oscaromeu/FMCW-Radar/Testing/ampli/POWERS11.CSV

# Channel 1
# Trace 1
Power | Formatted Data | Formatted Data
-2.00000000000E+001 | +4.50951344603E+001 | +1.51865665357E+001
-1.92187500000E+001 | +4.50790566312E+001 | +1.52116471144E+001
-1.84375000000E+001 | +4.50726827151E+001 | +1.52351928487E+001
-1.76562500000E+001 | +4.50690425969E+001 | +1.52613131889E+001
-1.68750000000E+001 | +4.50613673300E+001 | +1.52756773957E+001
-1.60937500000E+001 | +4.50555678872E+001 | +1.52944158332E+001
-1.53125000000E+001 | +4.50582695477E+001 | +1.53212152465E+001
-1.45312500000E+001 | +4.50556417096E+001 | +1.53492725816E+001
-1.37500000000E+001 | +4.50490764386E+001 | +1.53702875242E+001
-1.29687500000E+001 | +4.50503405595E+001 | +1.53933060736E+001
-1.21875000000E+001 | +4.50435028047E+001 | +1.54296293869E+001
-1.14062500000E+001 | +4.50314186173E+001 | +1.54656649591E+001
-1.06250000000E+001 | +4.50133551086E+001 | +1.55094450594E+001
-9.84375000000E+000 | +4.49976467125E+001 | +1.55606128826E+001
-9.06250000000E+000 | +4.49709219796E+001 | +1.56371129033E+001
-8.28125000000E+000 | +4.49330093634E+001 | +1.57325963698E+001
-7.50000000000E+000 | +4.48811782491E+001 | +1.58564781718E+001
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
