oscaromeu/FMCW-Radar/Testing/vco/vco.pdf

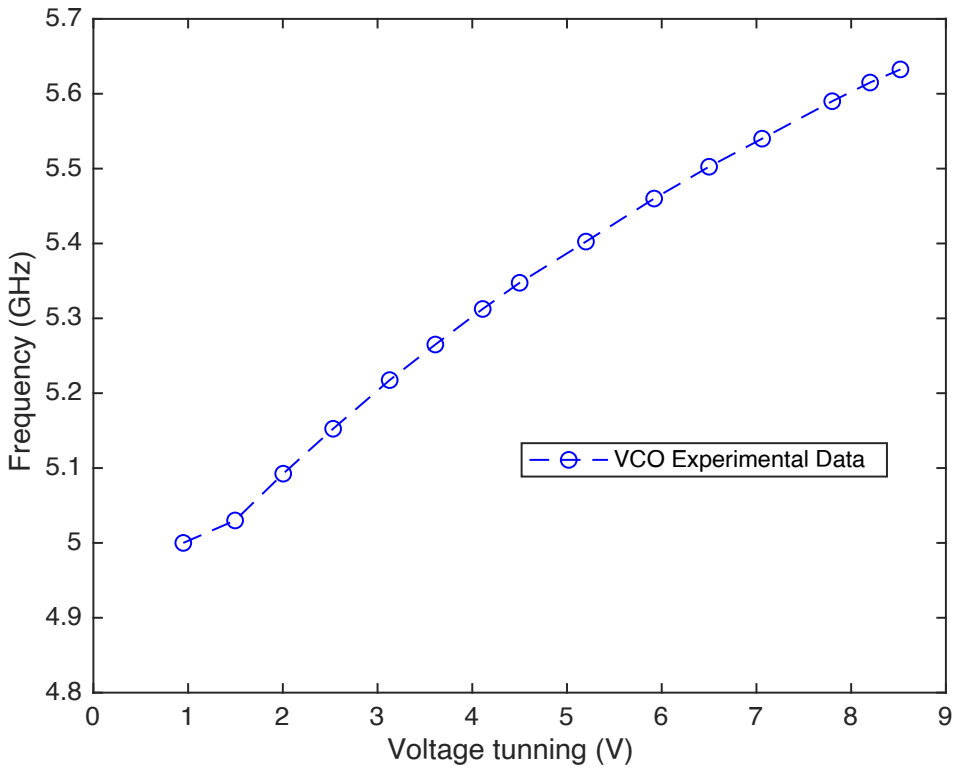
[picture p21: page 1]
Voltage tunning (V); Frequency (GHz)

VCO Experimental Data
