oscaromeu/FMCW-Radar/Hardware/FMCWRadar/doc/FMCWRadar_sch.pdf

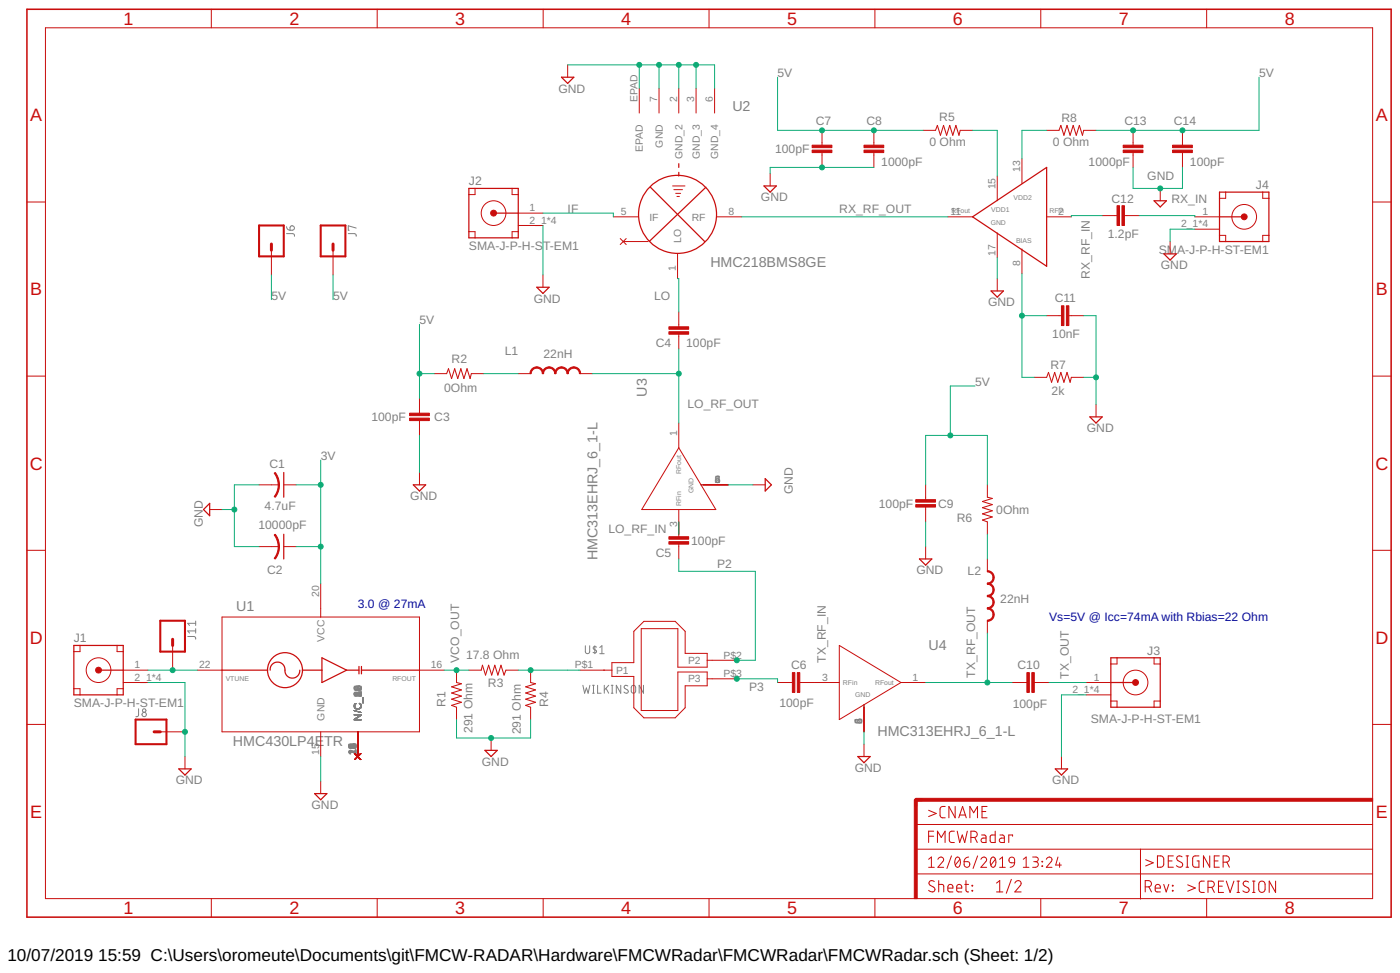
[picture p22: page 1]

Vs=5V @ Icc=74mA with Rbias=22 Ohm

10/07/2019 15:59 C:\Users\oromeute\Documents\git\FMCW-RADAR\Hardware\FMCWRadar\FMCWRadar\FMCWRadar.sch (Sheet: 1/2)

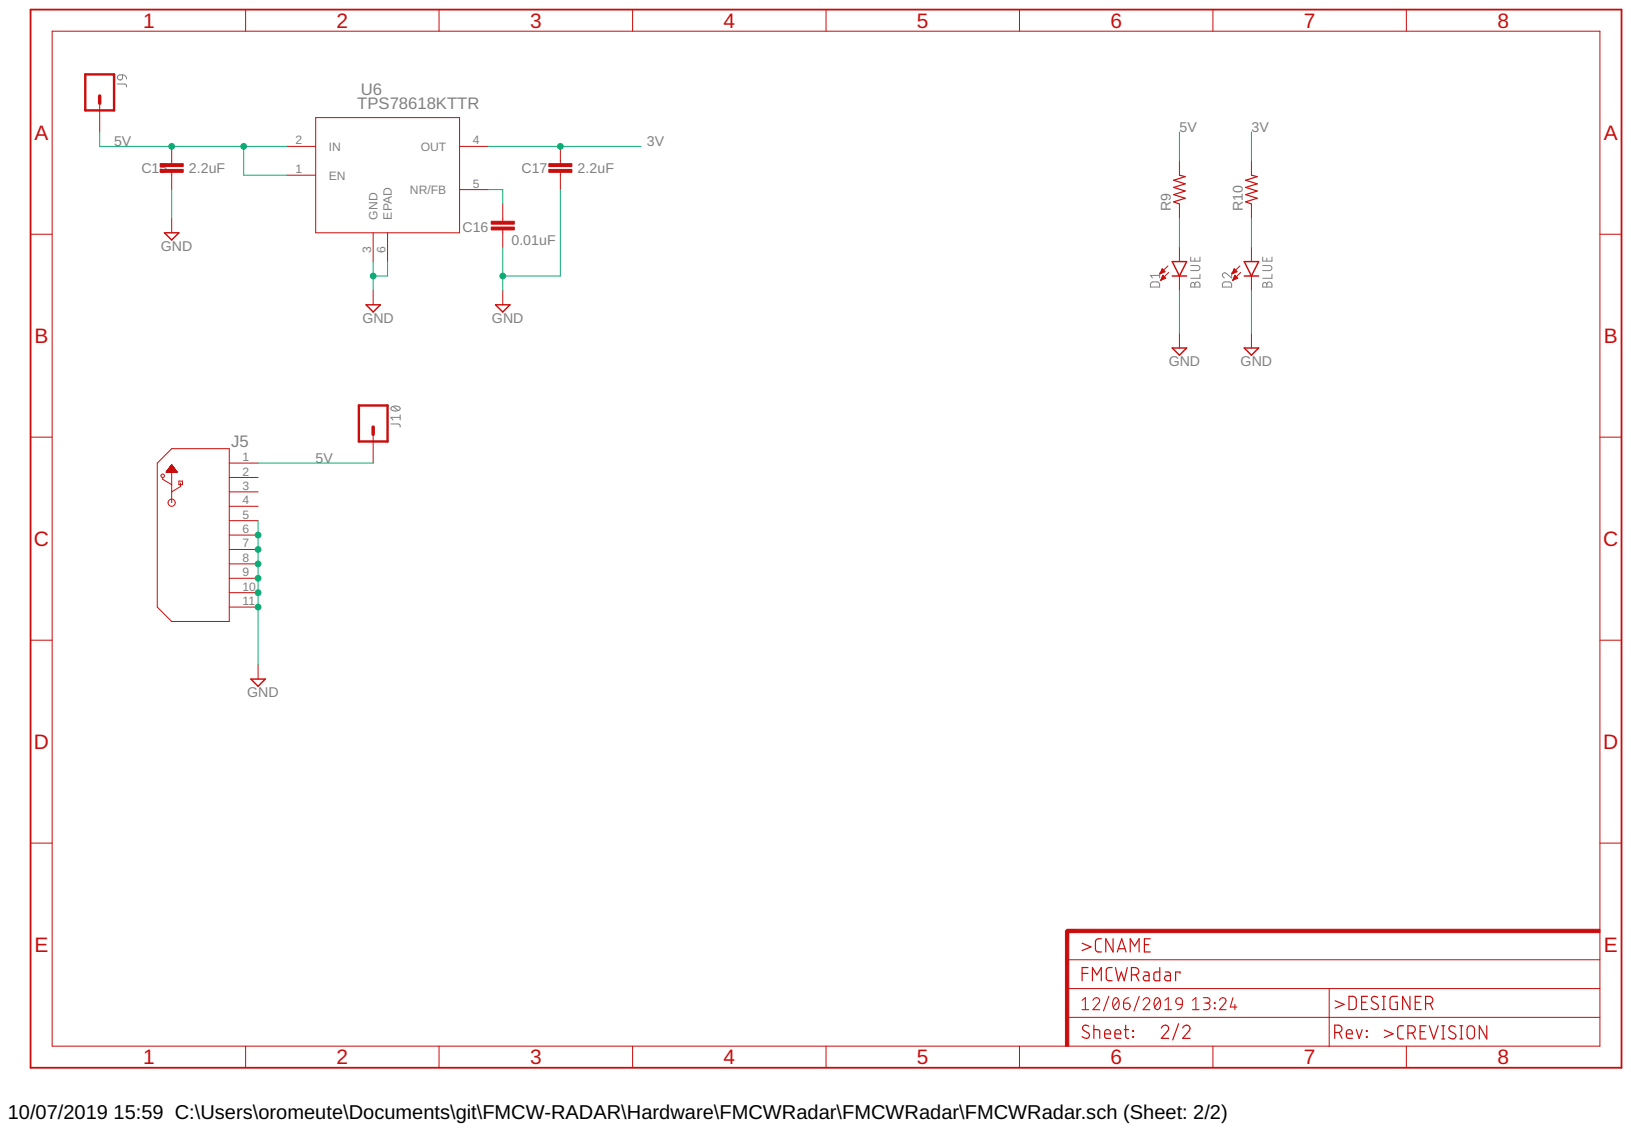
[picture p23: page 2]

10/07/2019 15:59 C:\Users\oromeute\Documents\git\FMCW-RADAR\Hardware\FMCWRadar\FMCWRadar\FMCWRadar.sch (Sheet: 2/2)
