oscaromeu/FMCW-Radar/Hardware/FMCWRadar/FMCWRadar/FMCWRadar.pdf

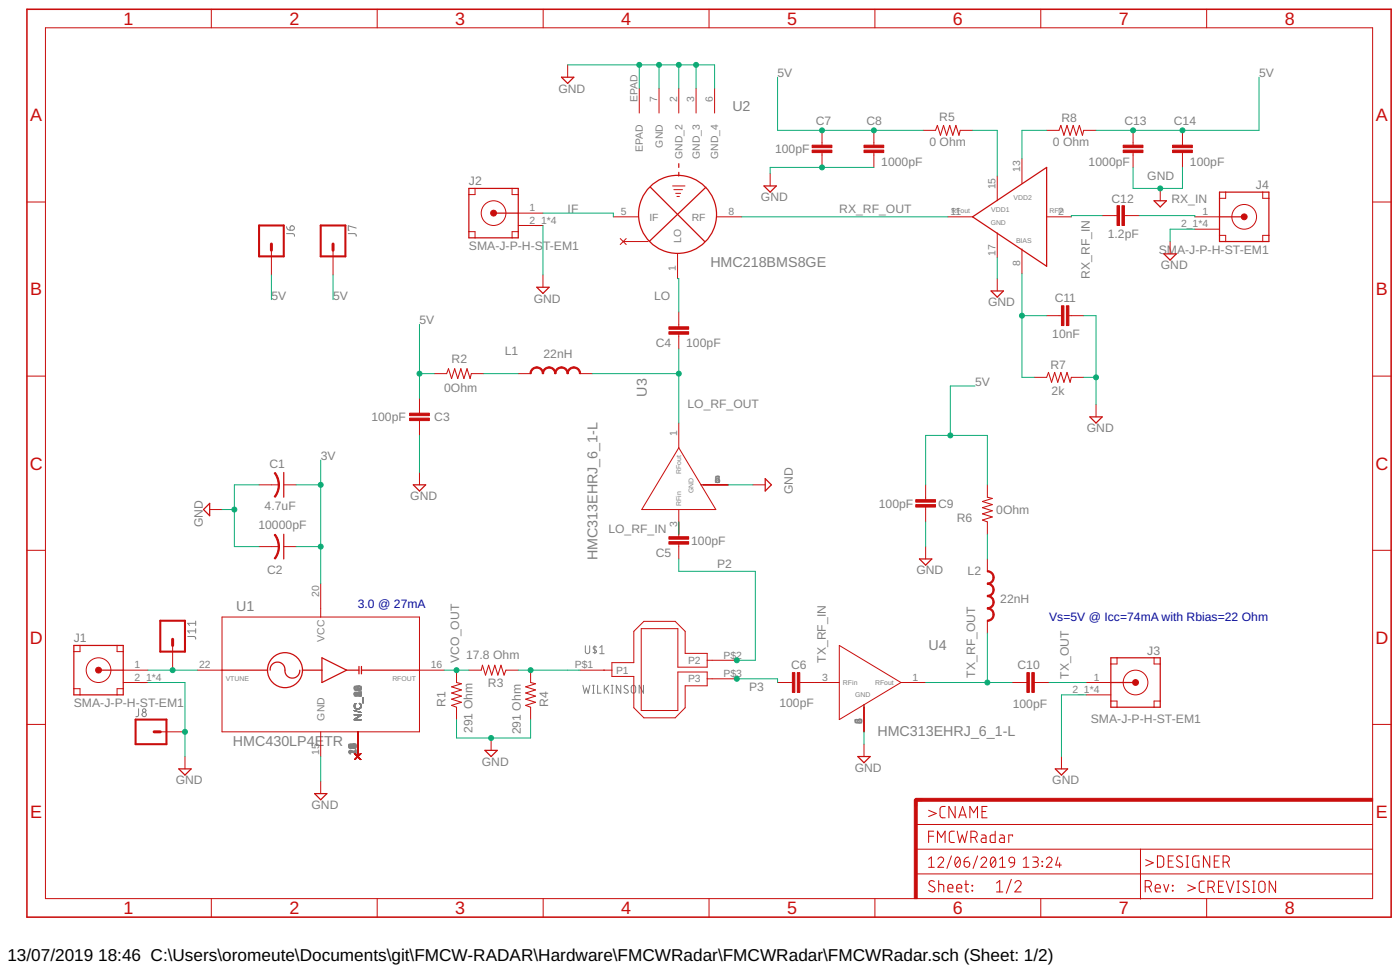
[picture p24: page 1]

Vs=5V @ Icc=74mA with Rbias=22 Ohm

13/07/2019 18:46 C:\Users\oromeute\Documents\git\FMCW-RADAR\Hardware\FMCWRadar\FMCWRadar\FMCWRadar.sch (Sheet: 1/2)
