oscaromeu/FMCW-Radar/Testing/vivaldi/vivaldi1.pdf

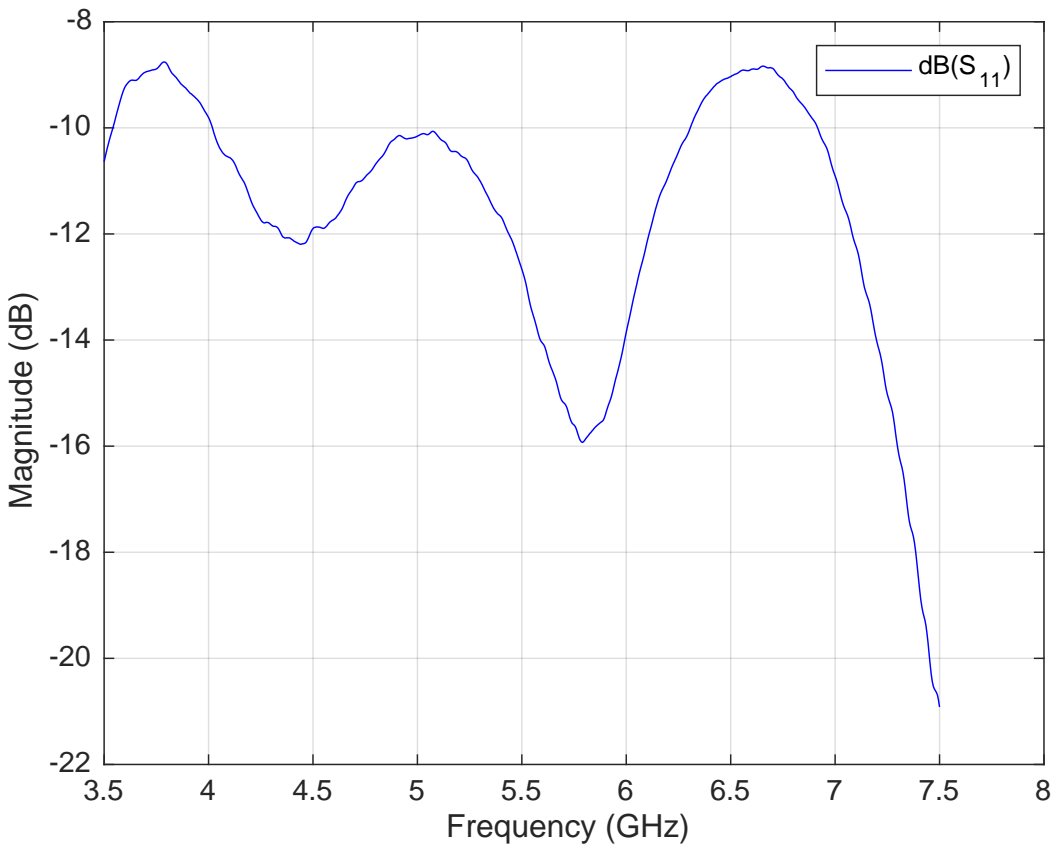
[picture p28: page 1]
Frequency (GHz); Magnitude (dB)
