oscaromeu/FMCW-Radar/Testing/vivaldi/vivaldi12_s11_s12_metal.pdf

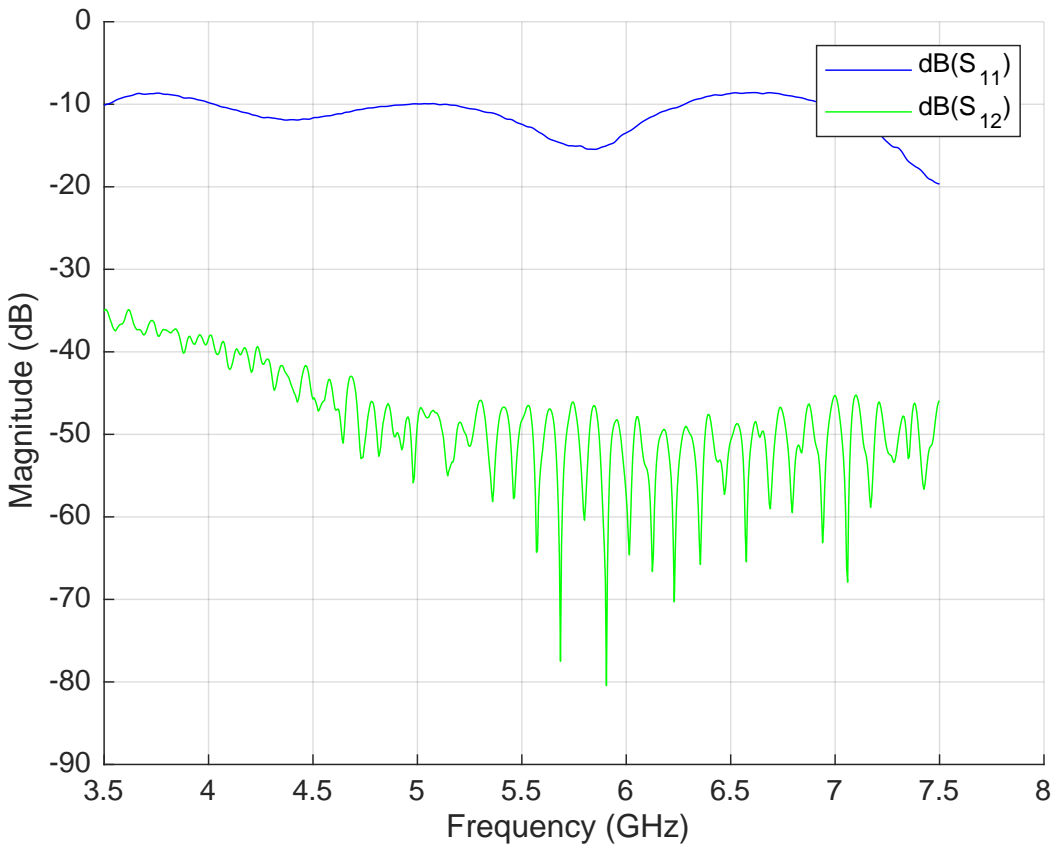
[picture p29: page 1]
Frequency (GHz); Magnitude (dB)

dB(S11 | ) )
dB(S12
