oscaromeu/FMCW-Radar/Testing/vivaldi/vivaldi12_s11_s12_sinmetal.pdf

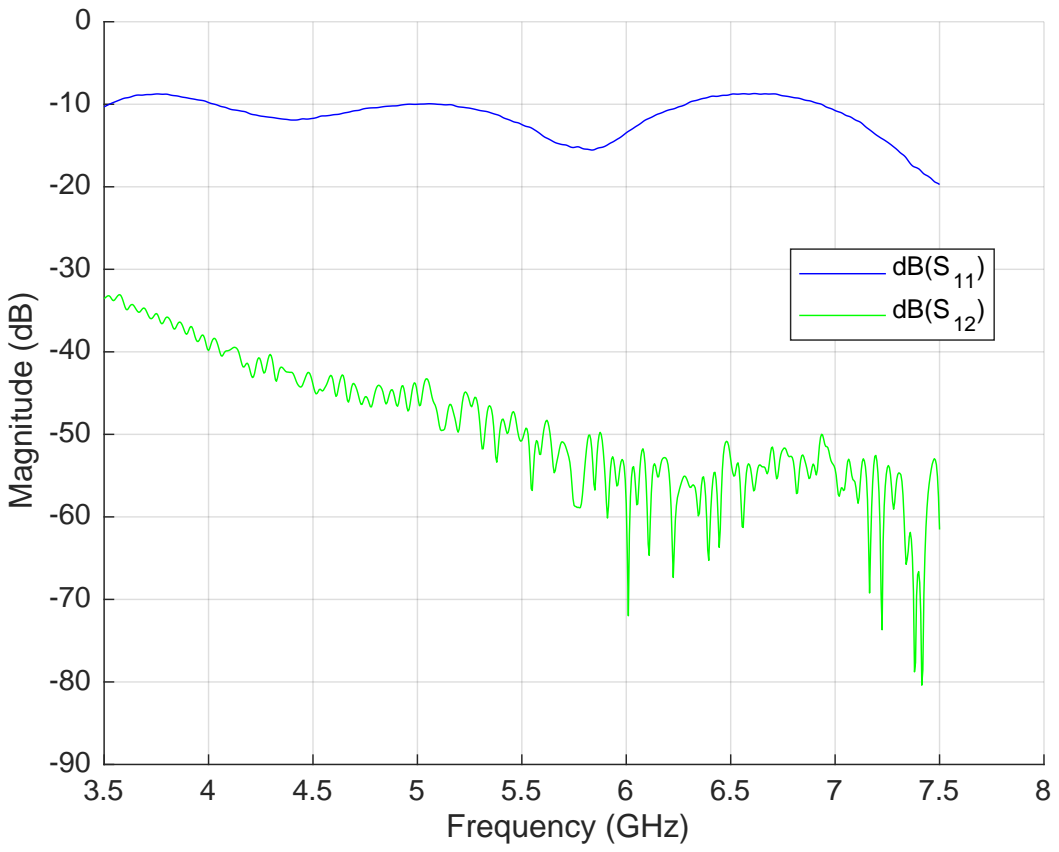
[picture p30: page 1]
Frequency (GHz); Magnitude (dB)

dB(S11)
dB(S12)
