oscaromeu/FMCW-Radar/Testing/vivaldi/vivaldi12_s12_s11.pdf

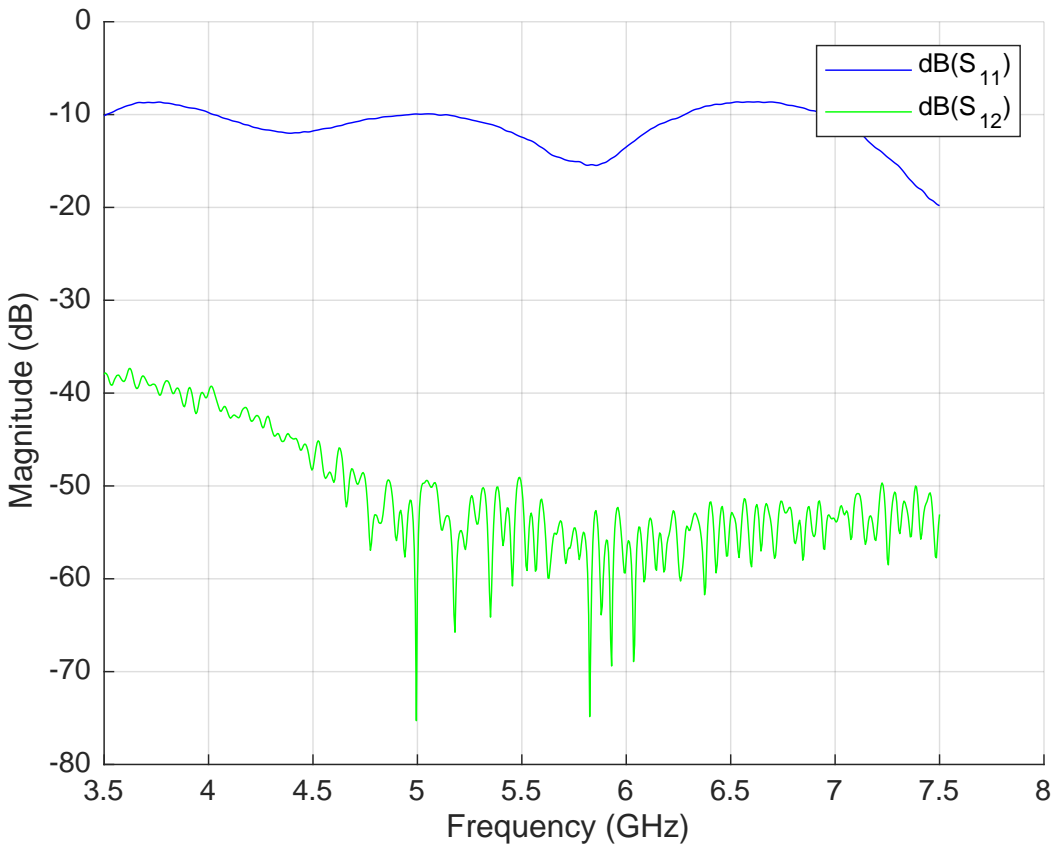
[picture p31: page 1]
Frequency (GHz); Magnitude (dB)
