oscaromeu/FMCW-Radar/Testing/vivaldi/vivaldi12_s12_s11_frontal.pdf

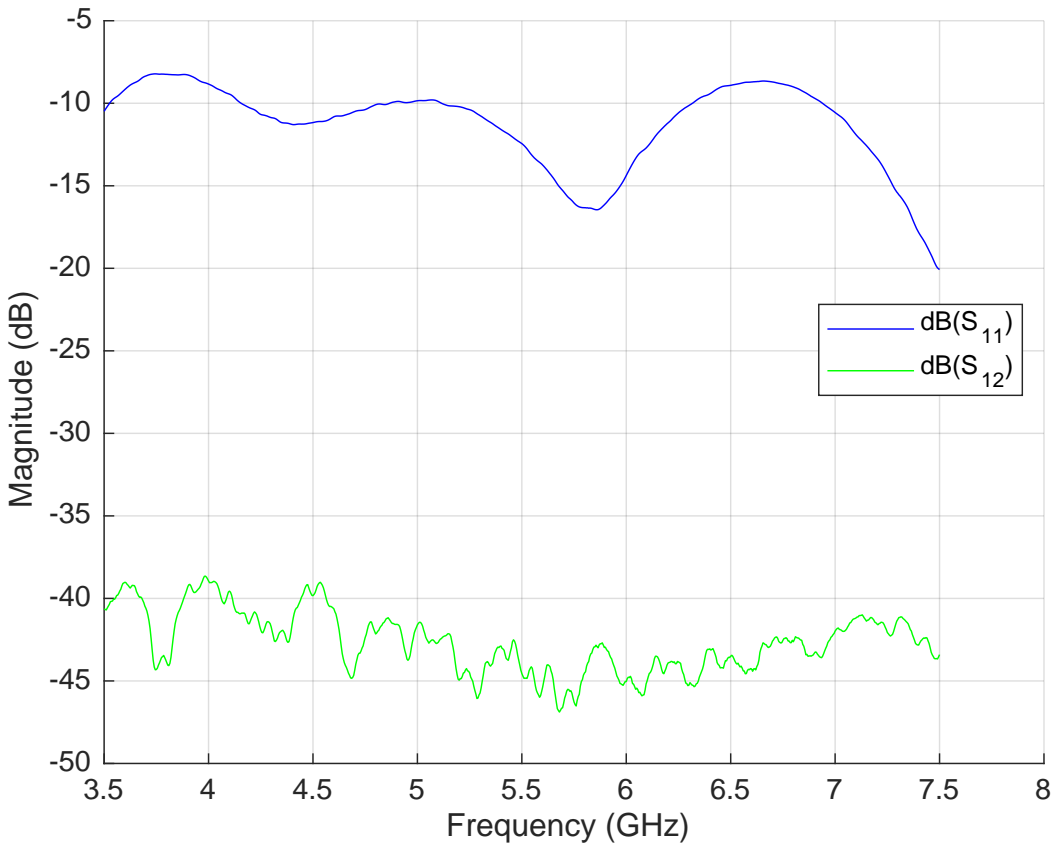
[picture p32: page 1]
Frequency (GHz); Magnitude (dB)

dB(S11)
dB(S12)
