oscaromeu/FMCW-Radar/Testing/vivaldi/vivaldi12_s21_s22.pdf

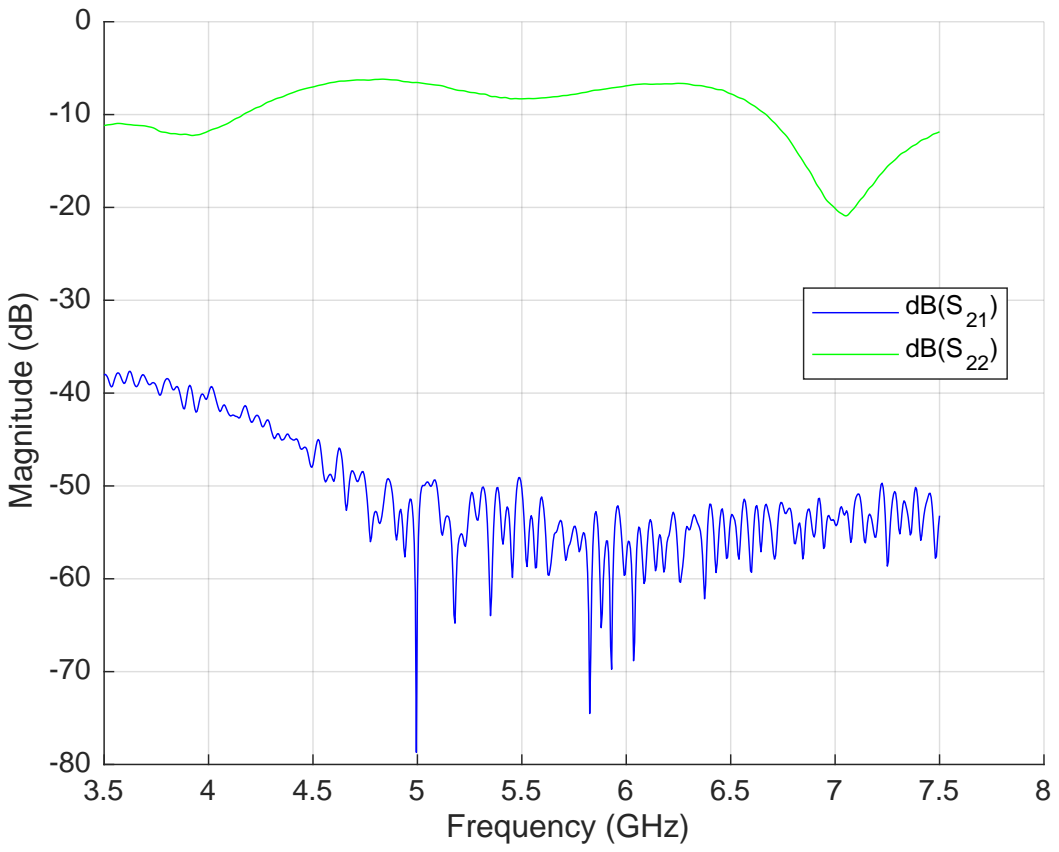
[picture p33: page 1]
Frequency (GHz); Magnitude (dB)
