oscaromeu/FMCW-Radar/Testing/vivaldi/vivaldi12_s21_s22_frontal.pdf

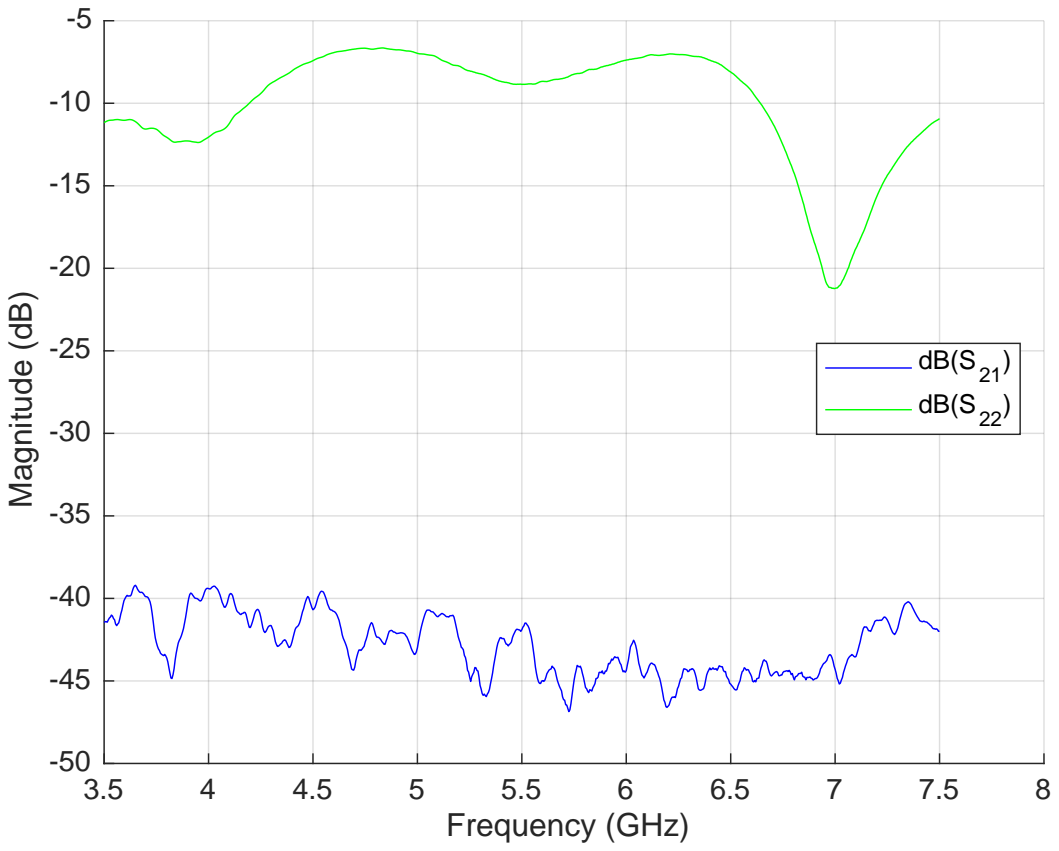
[picture p34: page 1]
Frequency (GHz); Magnitude (dB)
