oscaromeu/FMCW-Radar/Testing/vivaldi/vivaldi12_s21_s22_sin_metal.pdf

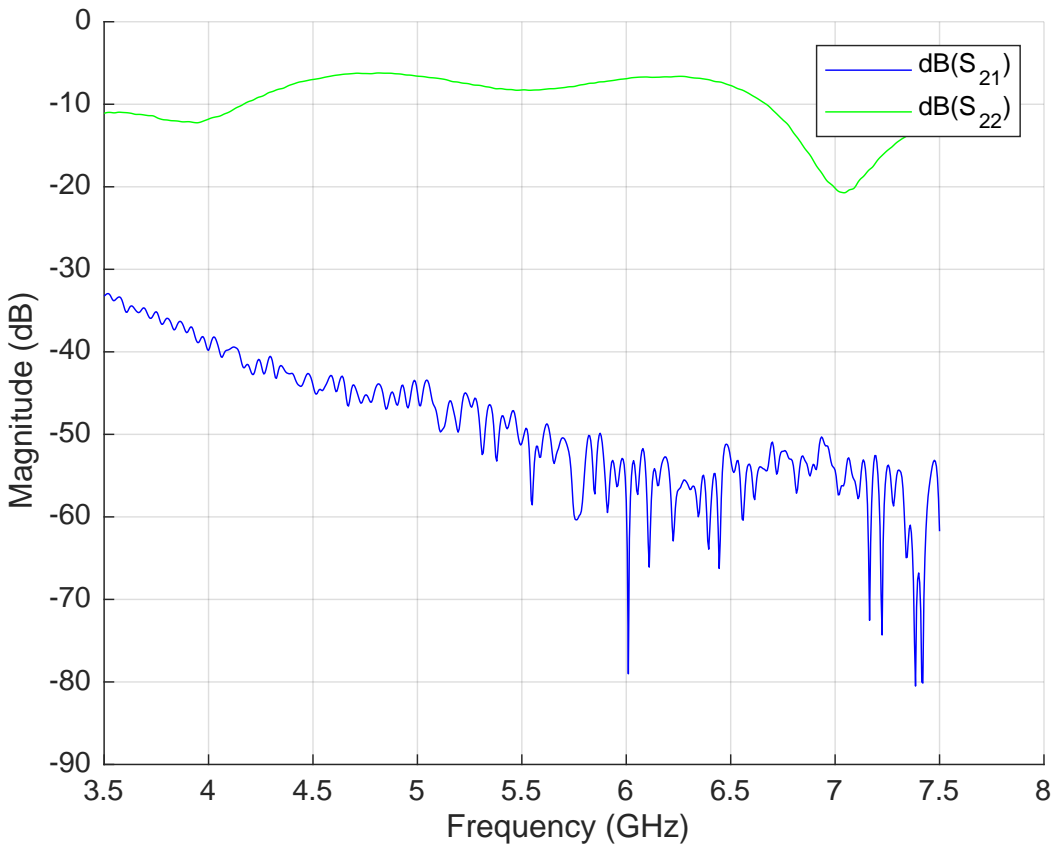
[picture p36: page 1]
Frequency (GHz); Magnitude (dB)

dB(S21 | ) )
dB(S22
