oscaromeu/FMCW-Radar/Testing/vivaldi/vivaldi2.pdf

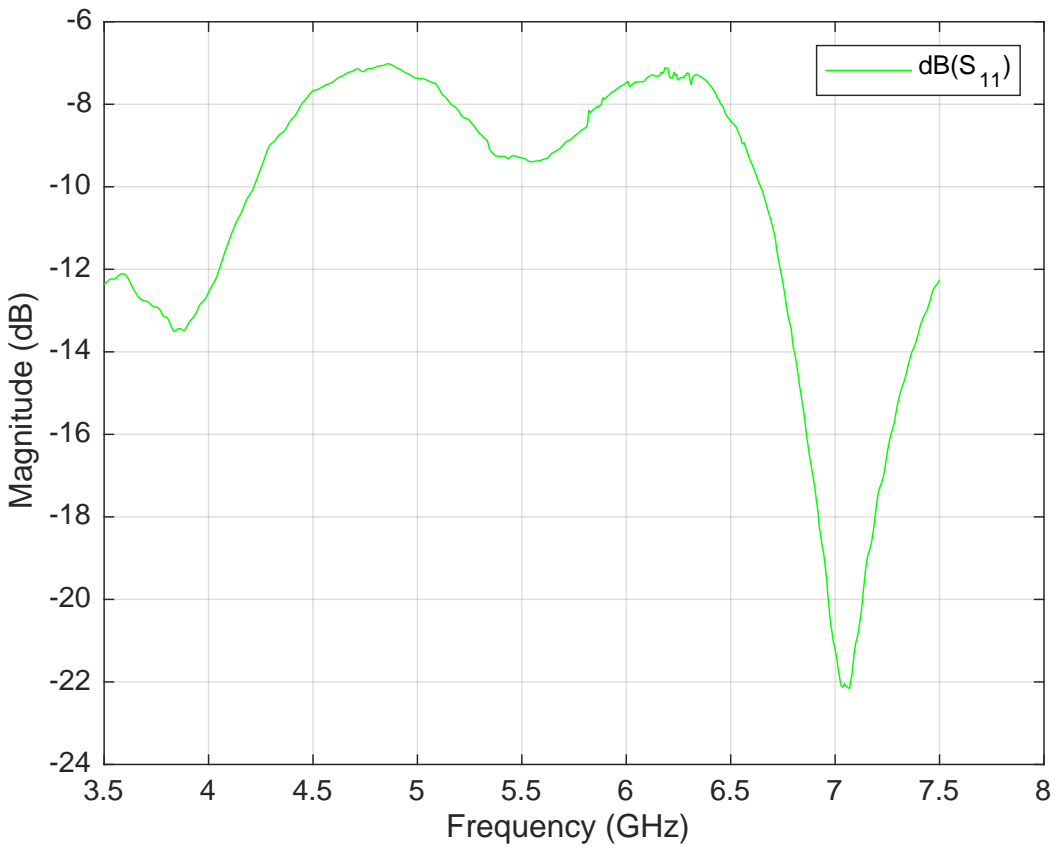
[picture p37: page 1]
Frequency (GHz); Magnitude (dB)
