oscaromeu/FMCW-Radar/Testing/vivaldi/vivaldi3.pdf

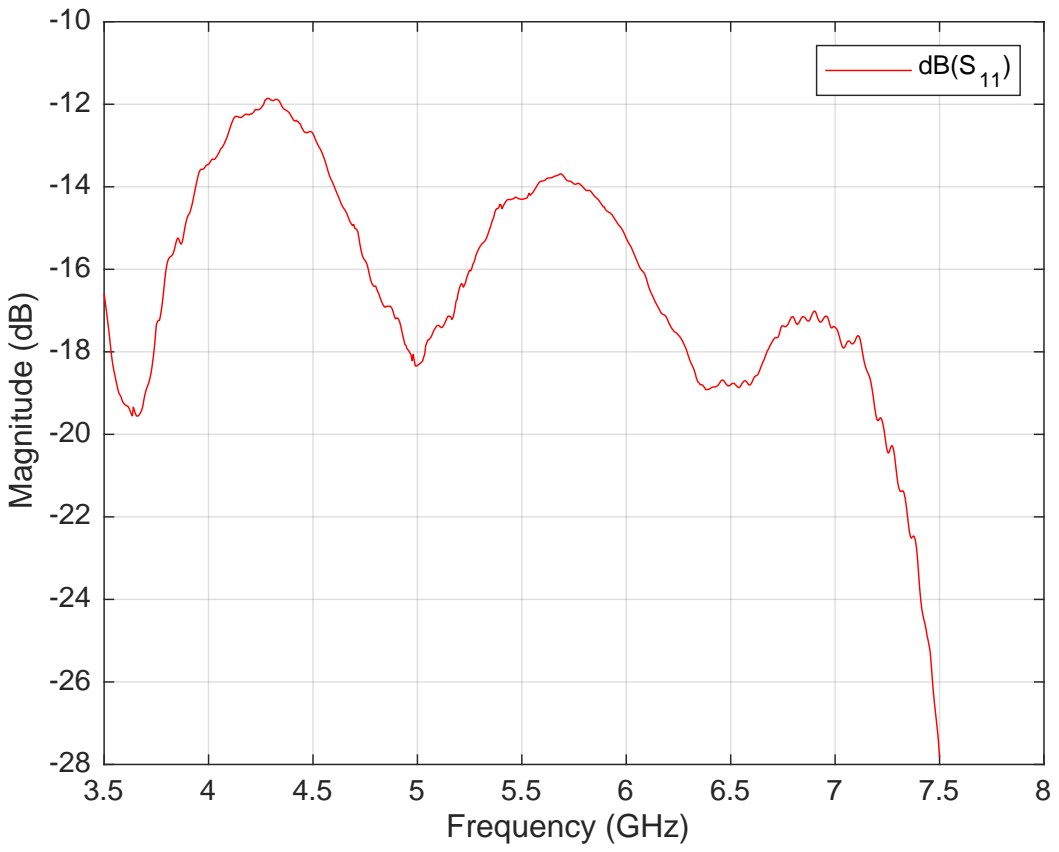
[picture p38: page 1]
Frequency (GHz); Magnitude (dB)
