oscaromeu/FMCW-Radar/Testing/wilkinson/insertionLoss.pdf

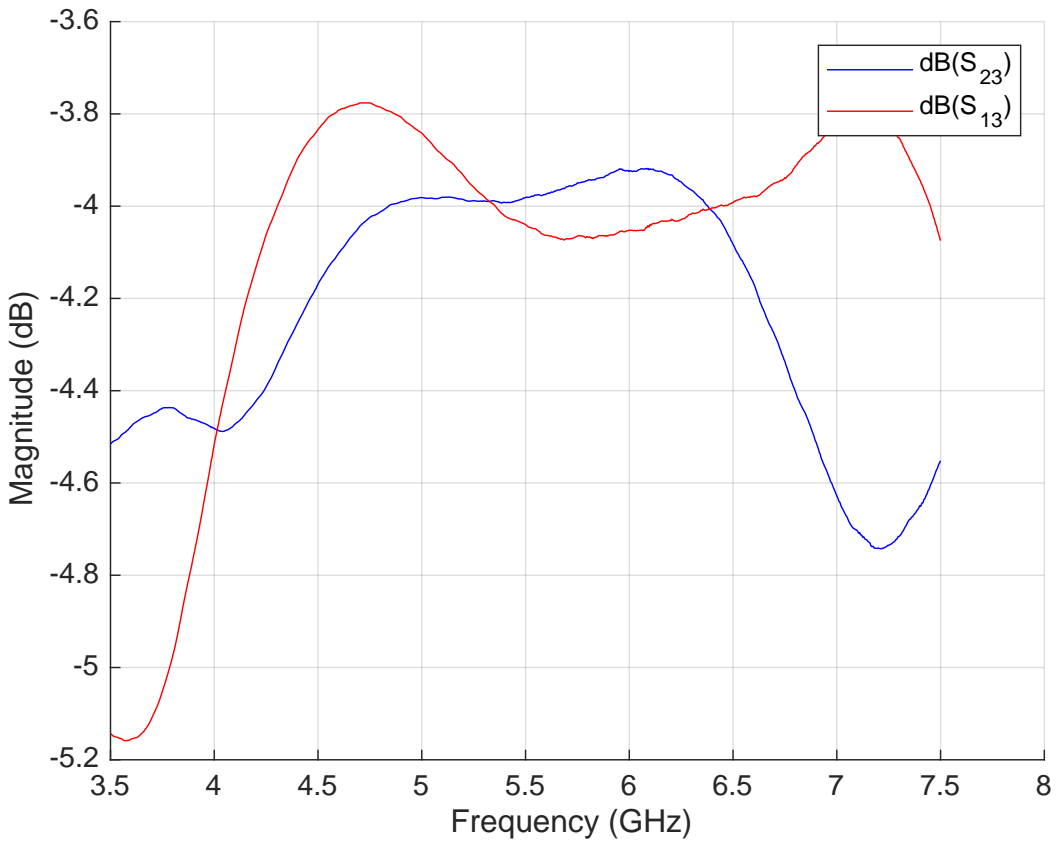
[picture p39: page 1]
Frequency (GHz); Magnitude (dB)
