oscaromeu/FMCW-Radar/Testing/wilkinson/isolation.pdf

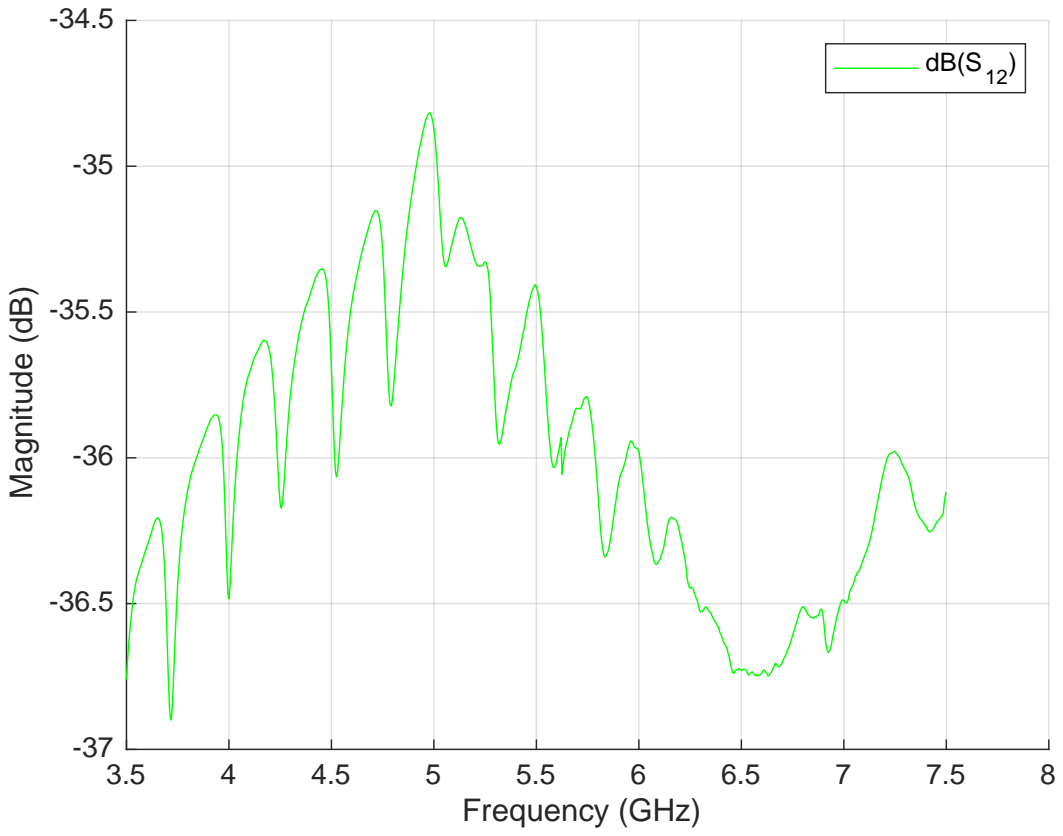
[picture p40: page 1]
Frequency (GHz); Magnitude (dB)
