oscaromeu/FMCW-Radar/Testing/wilkinson/returnLoss.pdf

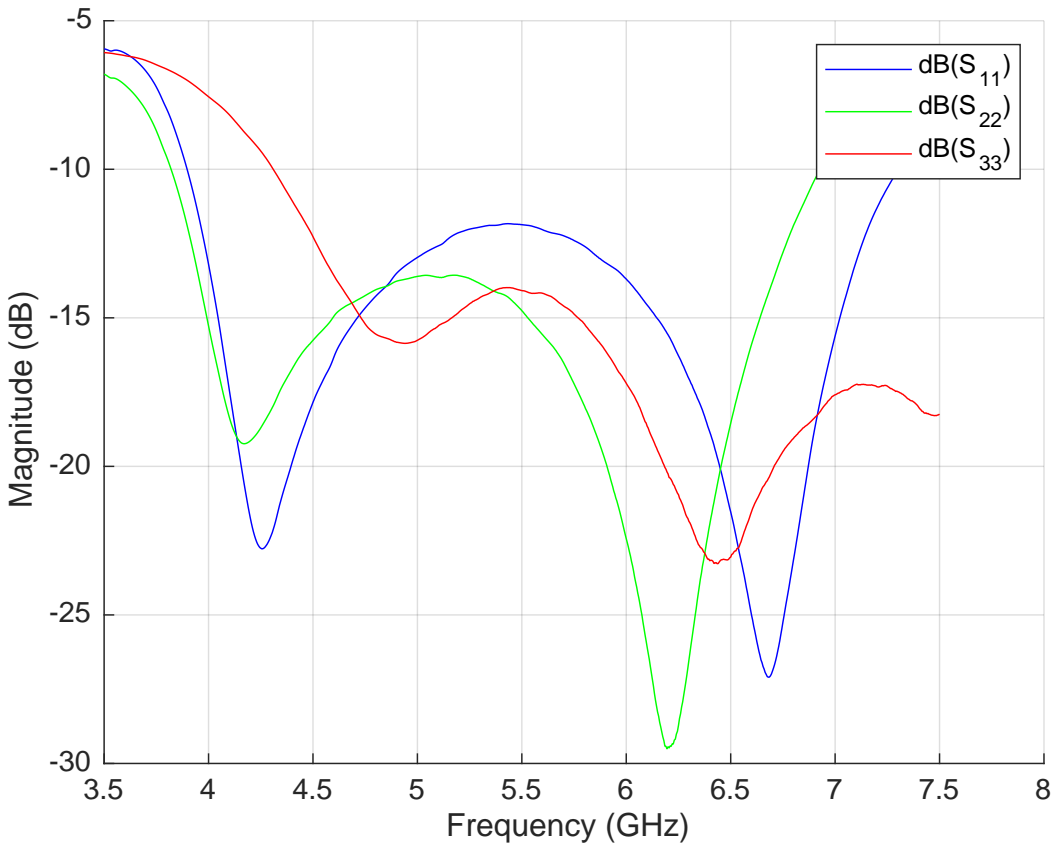
[picture p41: page 1]
Frequency (GHz); Magnitude (dB)
