oscaromeu/FMCW-Radar/Testing/wilkinson/wilkinson.pdf

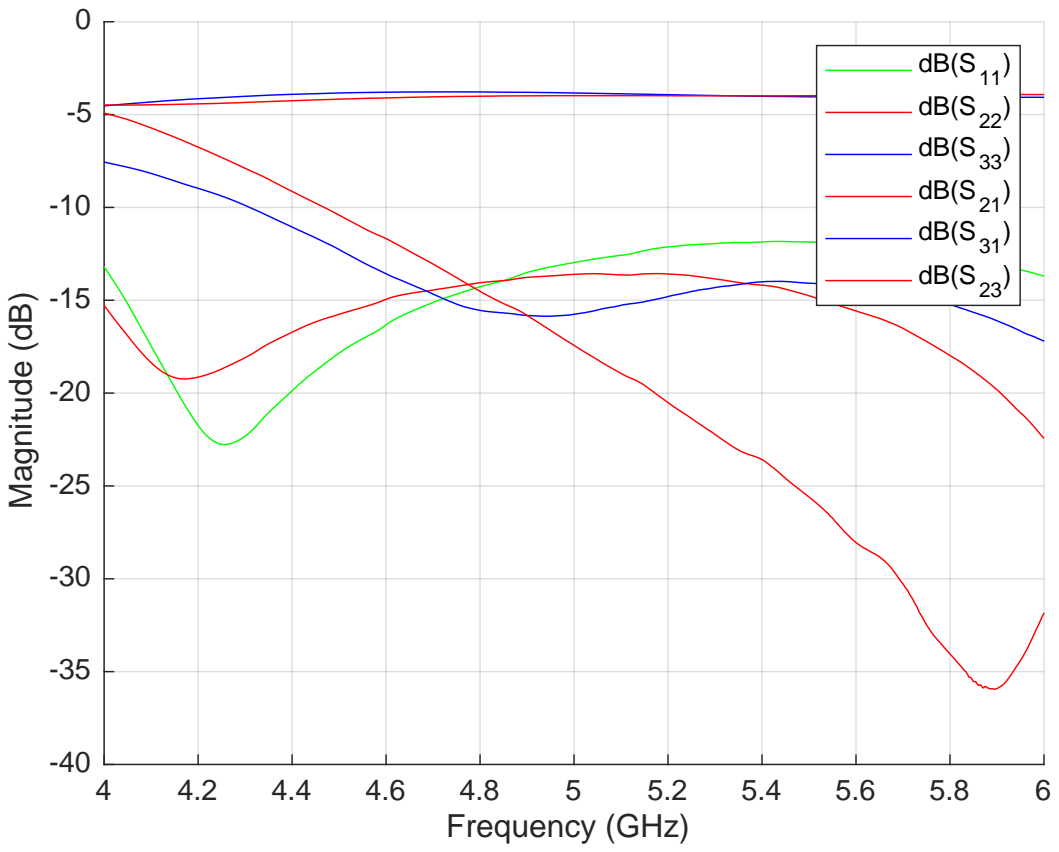
[picture p42: page 1]
Frequency (GHz); Magnitude (dB)
