oscaromeu/FMCW-Radar/Testing/wilkinson/wloads12.pdf

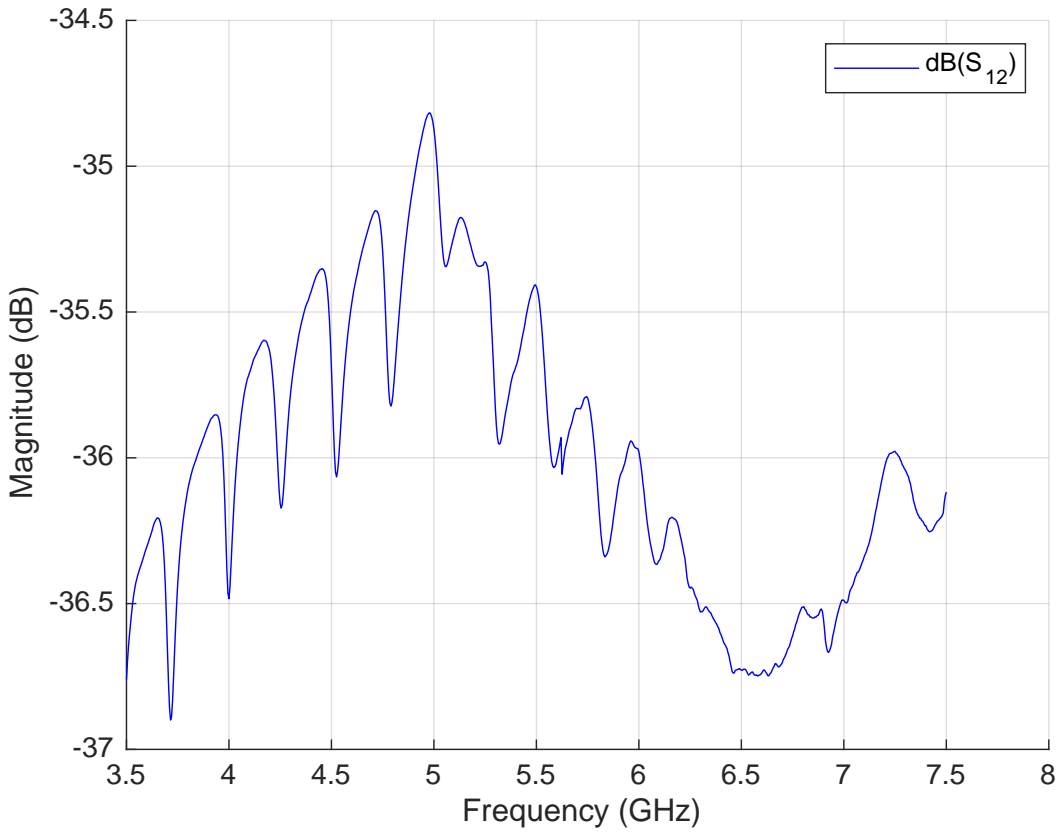
[picture p43: page 1]
Frequency (GHz); Magnitude (dB)
