oscaromeu/FMCW-Radar/Testing/wilkinson/wloads13.pdf

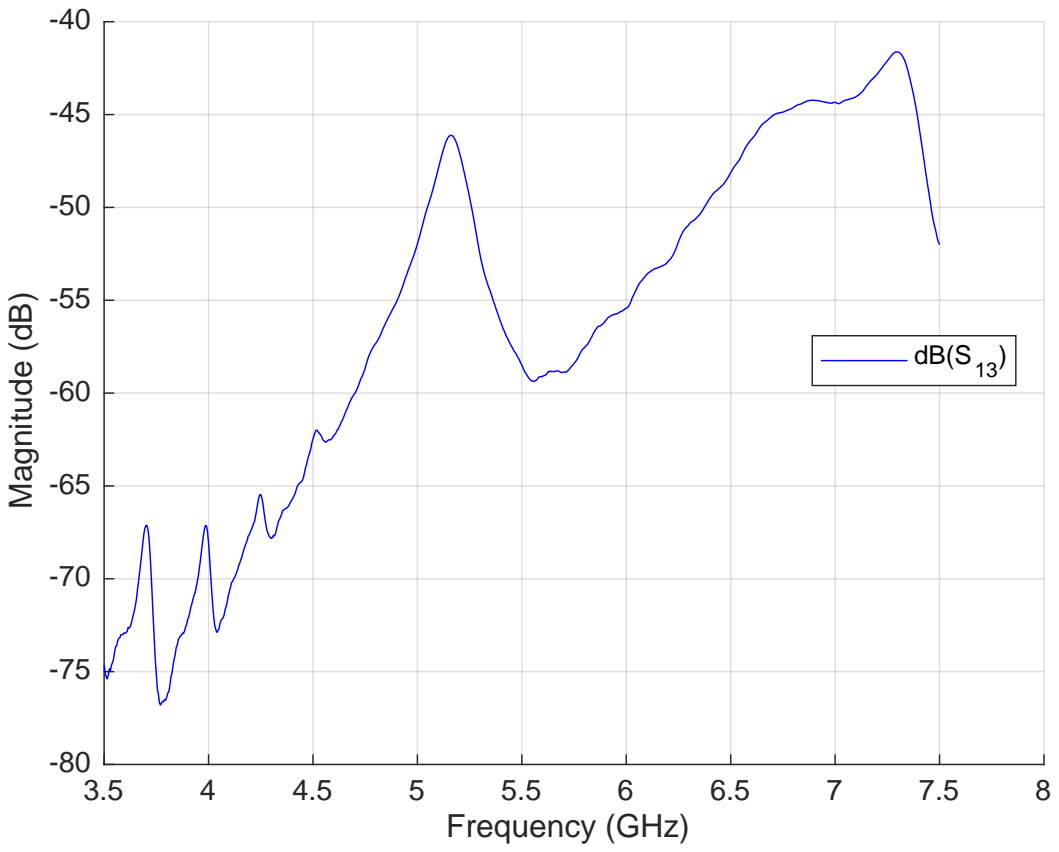
[picture p44: page 1]
Frequency (GHz); Magnitude (dB)
