oscaromeu/FMCW-Radar/Testing/wilkinson/wloads21.pdf

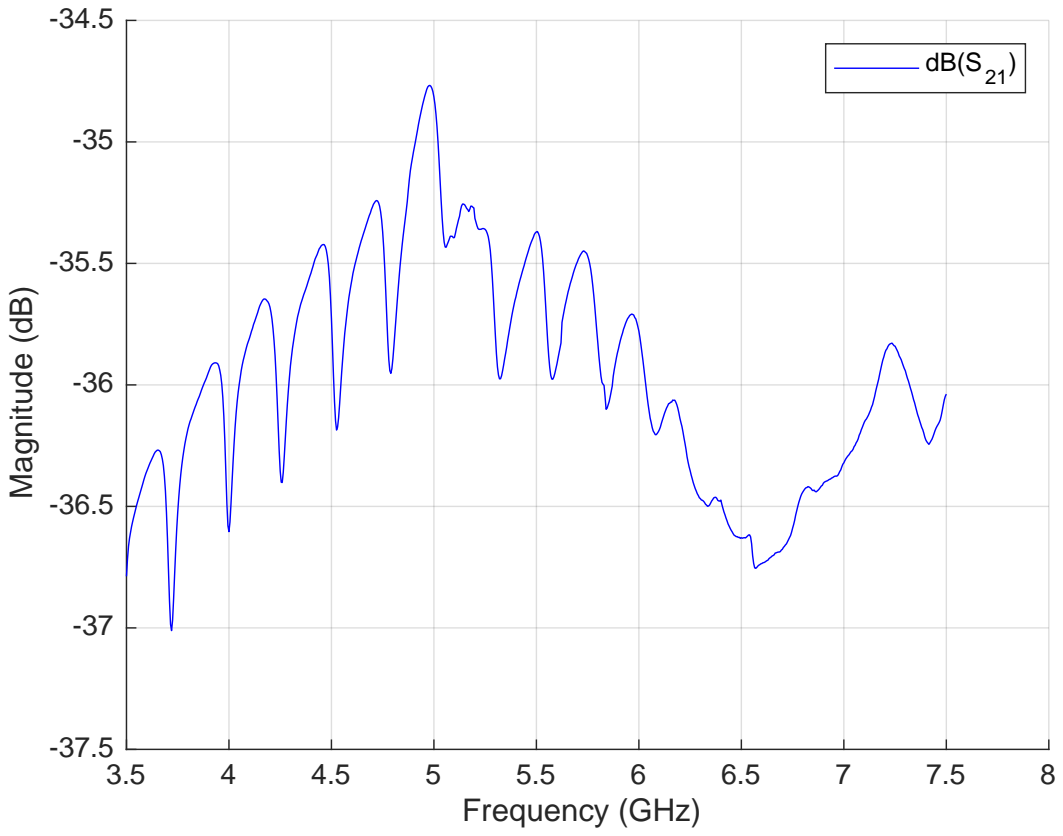
[picture p45: page 1]
Frequency (GHz); Magnitude (dB)
