oscaromeu/FMCW-Radar/Testing/wilkinson/wloads22.pdf

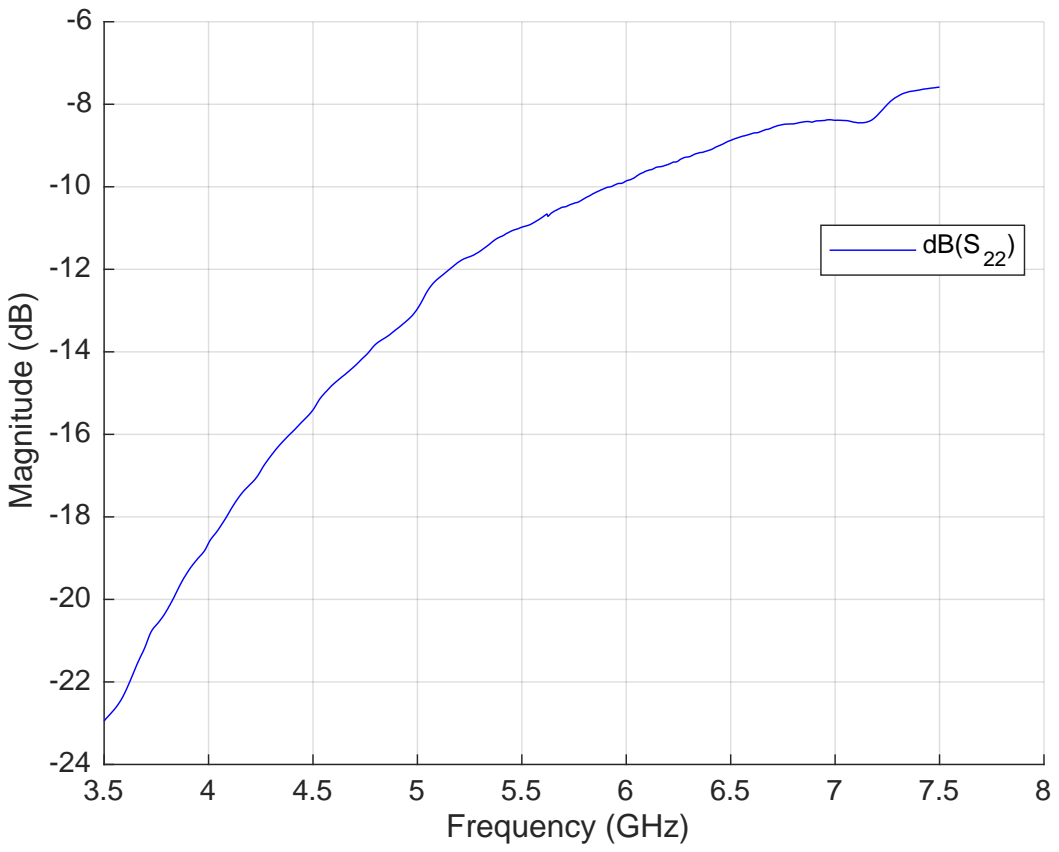
[picture p46: page 1]
Frequency (GHz); Magnitude (dB)
