oscaromeu/FMCW-Radar/Testing/wilkinson/wloads23.pdf

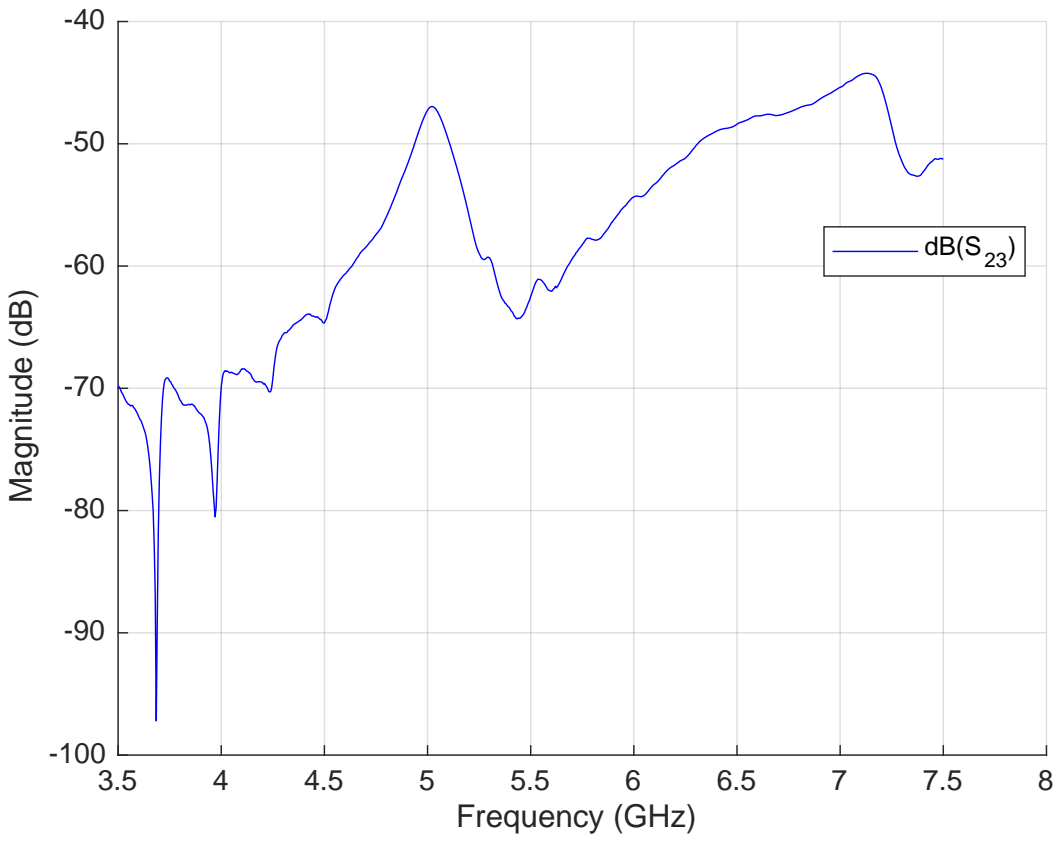
[picture p47: page 1]
Frequency (GHz); Magnitude (dB)
