oscaromeu/FMCW-Radar/Testing/wilkinson/wloads31.pdf

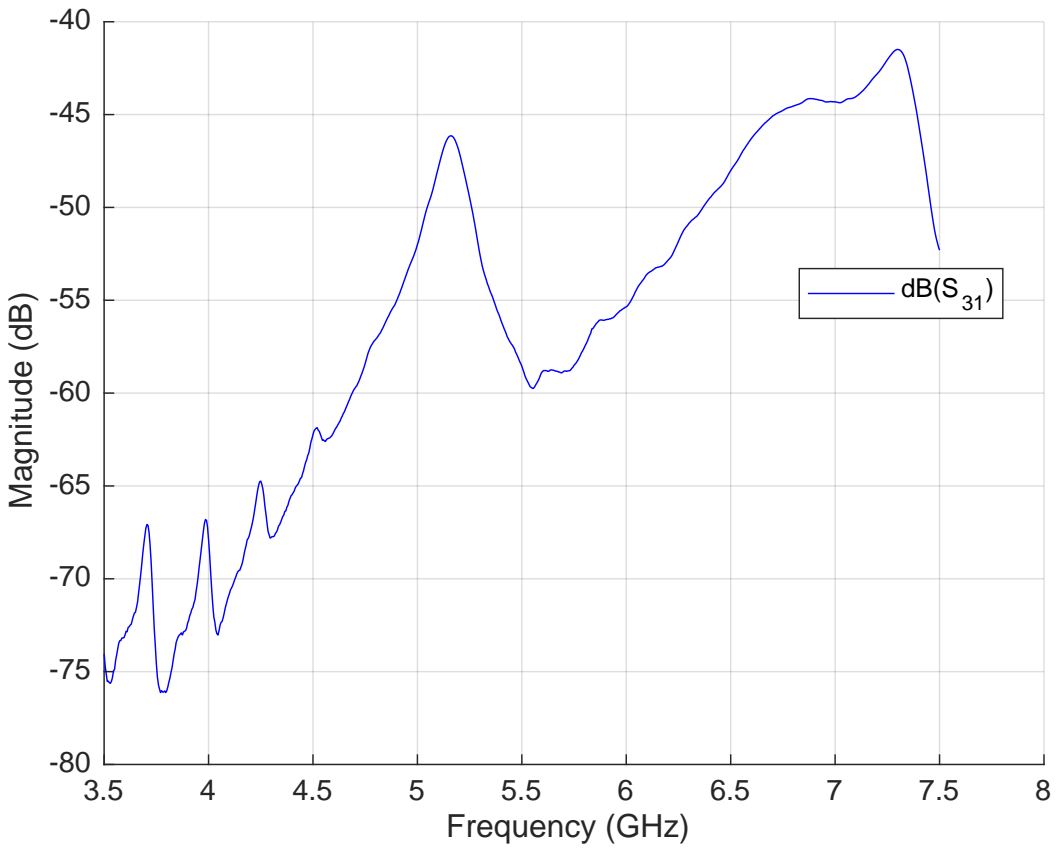
[picture p48: page 1]
Frequency (GHz); Magnitude (dB)
