oscaromeu/FMCW-Radar/Testing/wilkinson/wloads32.pdf

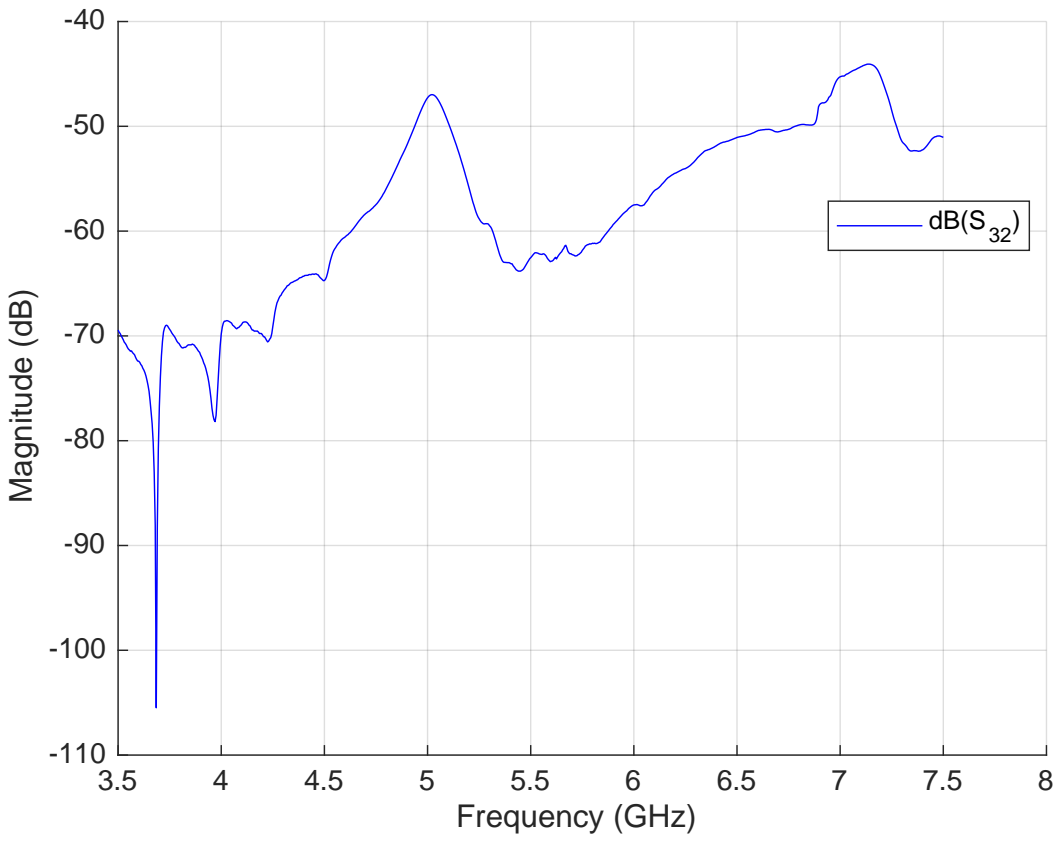
[picture p49: page 1]
Frequency (GHz); Magnitude (dB)
