oscaromeu/FMCW-Radar/Testing/wilkinson/wloads33.pdf

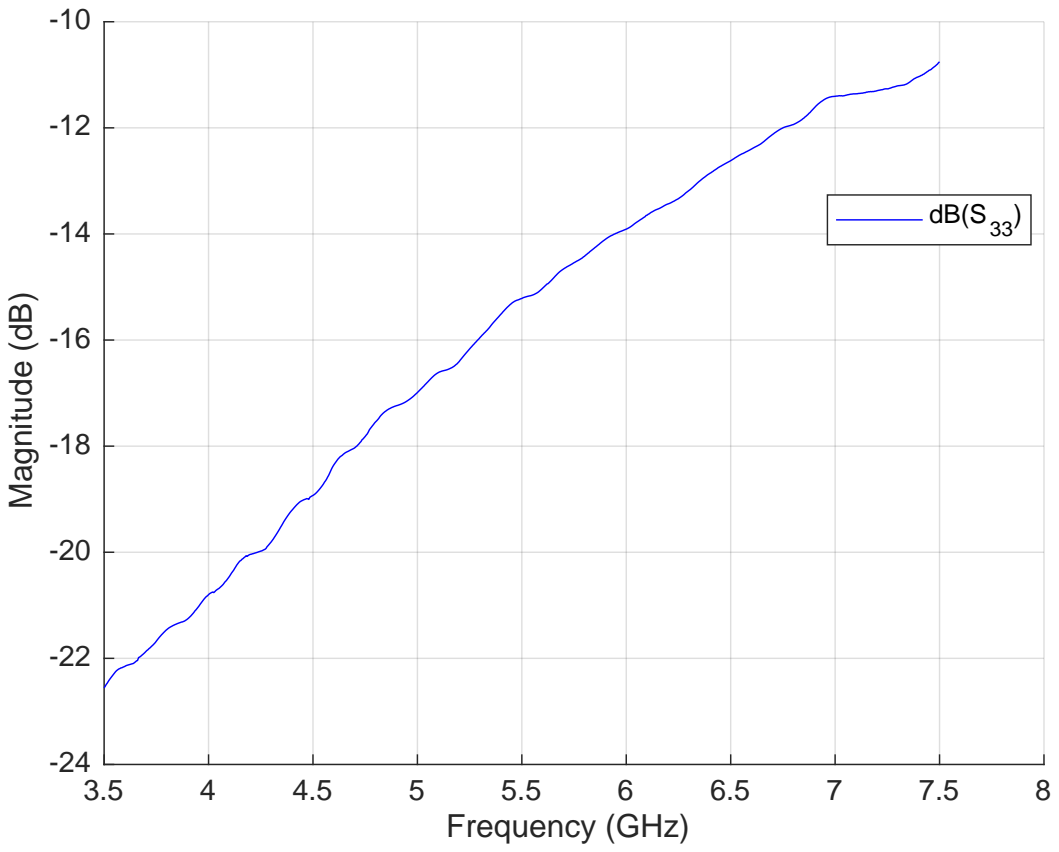
[picture p50: page 1]
Frequency (GHz); Magnitude (dB)
