oscaromeu/FMCW-Radar/Hardware/FMCWRadar/doc/FMCWRadar_layout.pdf

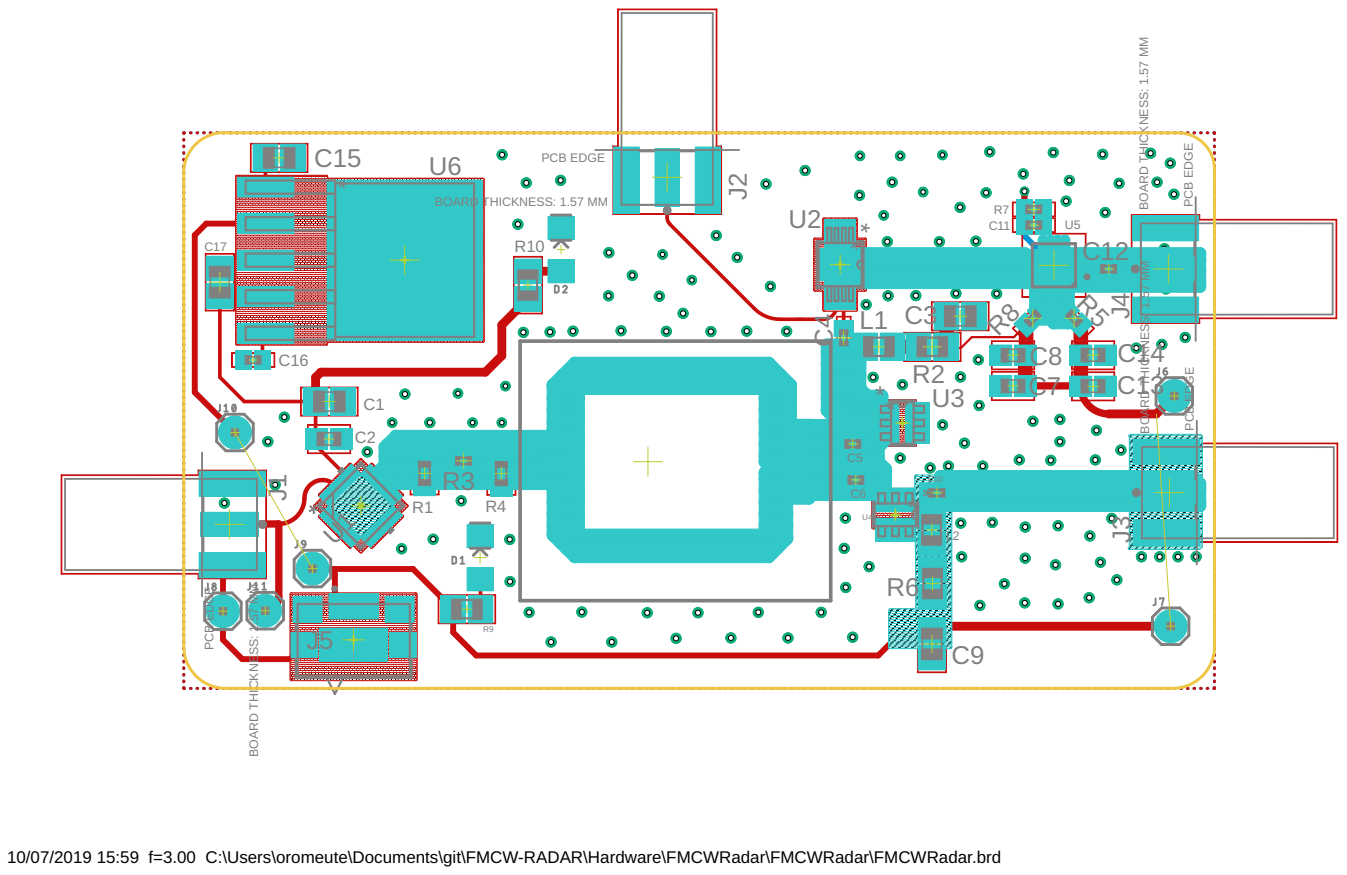
[picture p51: page 1]

10/07/2019 15:59 f=3.00 C:\Users\oromeute\Documents\git\FMCW-RADAR\Hardware\FMCWRadar\FMCWRadar\FMCWRadar.brd
