oscaromeu/FMCW-Radar/Hardware/GainBlock/_print/GainBlock_layout.pdf

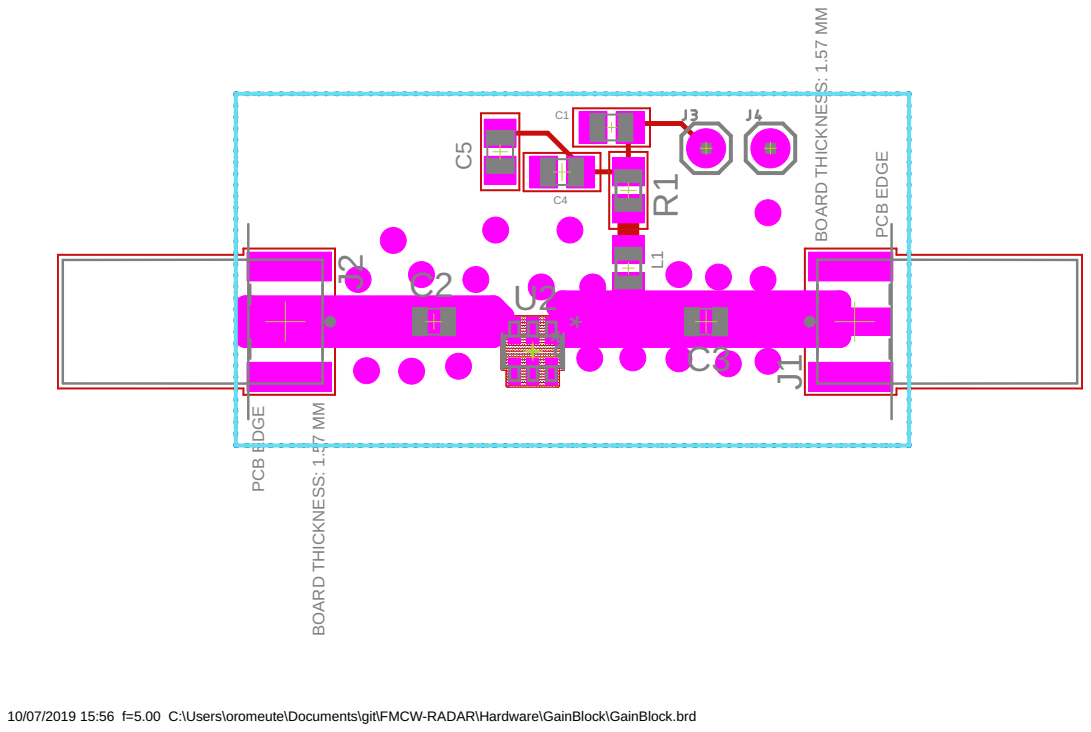
[picture p52: page 1]

10/07/2019 15:56 f=5.00 C:\Users\oromeute\Documents\git\FMCW-RADAR\Hardware\GainBlock\GainBlock.brd
