oscaromeu/FMCW-Radar/Hardware/GainBlock/_print/GainBlock_sch.pdf

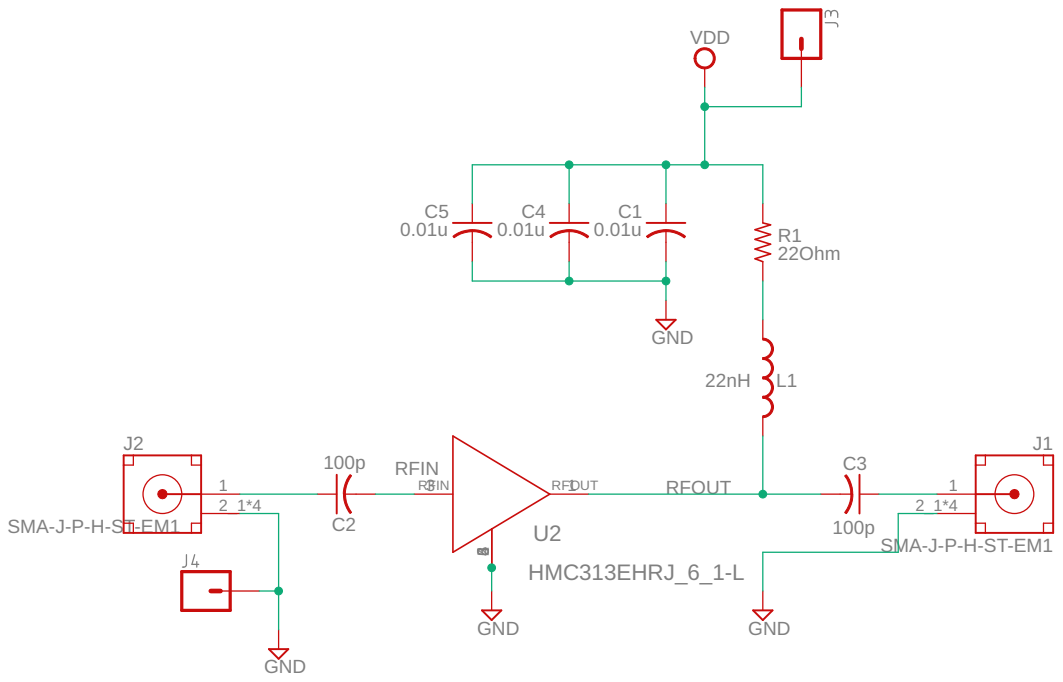
[picture p53: page 1]

10/07/2019 15:57 C:\Users\oromeute\Documents\git\FMCW-RADAR\Hardware\GainBlock\GainBlock.sch (Sheet: 1/1)
